sparkfun/SparkFun_GNSS_DAN-F10N/docs/assets/img/hookup_guide/ch340.png

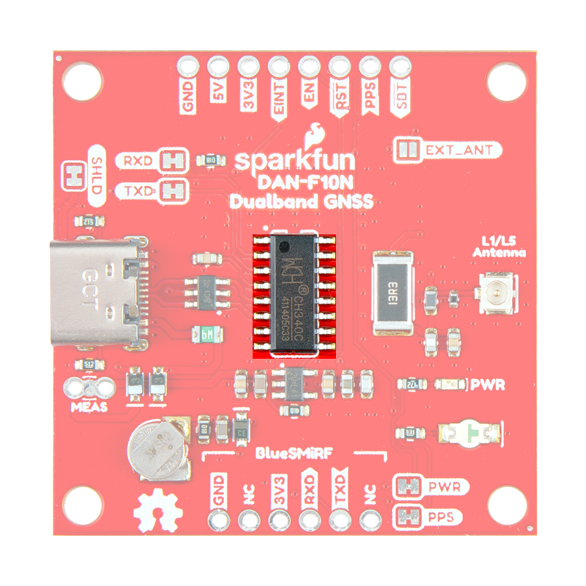
docs/assets/img/hookup_guide/ch340.png
