sparkfun/SparkFun_GNSS_DAN-F10N/docs/assets/img/hookup_guide/headers.png

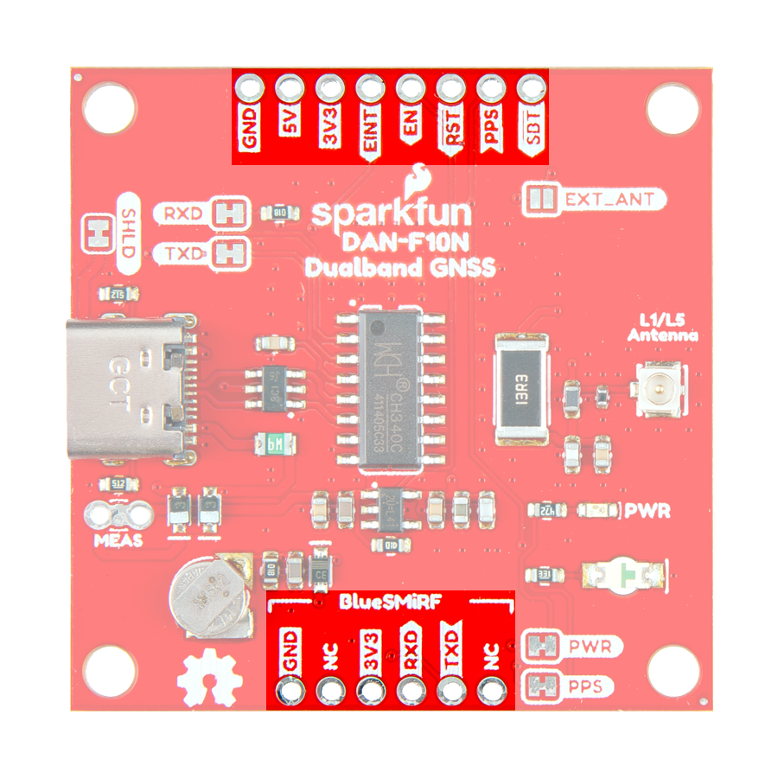
docs/assets/img/hookup_guide/headers.png
