sparkfun/SparkFun_GNSS_DAN-F10N/docs/assets/img/hookup_guide/periphrals_and_IO.png

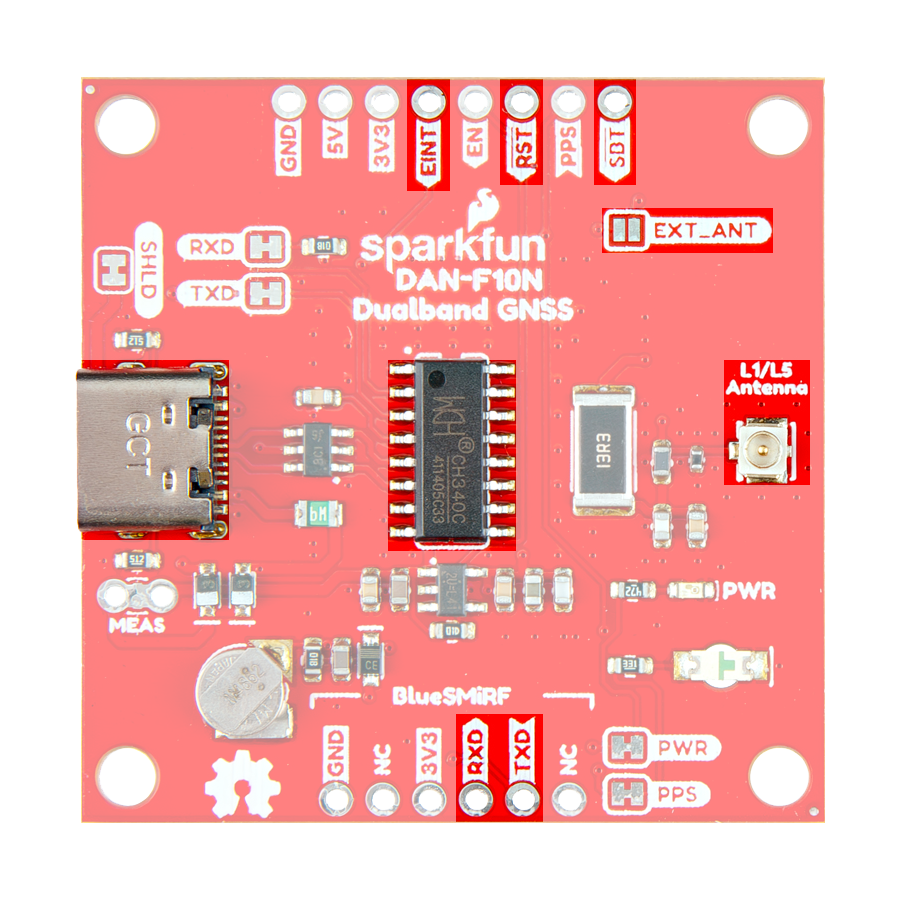
docs/assets/img/hookup_guide/periphrals_and_IO.png
